olonisakindavid/FinalYearProject/incubator - 2.jpg

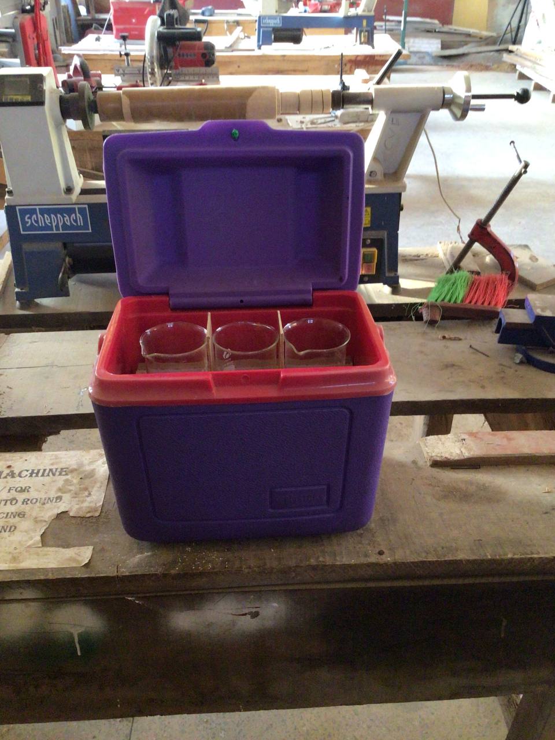
incubator - 2.jpg
