olonisakindavid/FinalYearProject/serial dht22 monitor.jpg

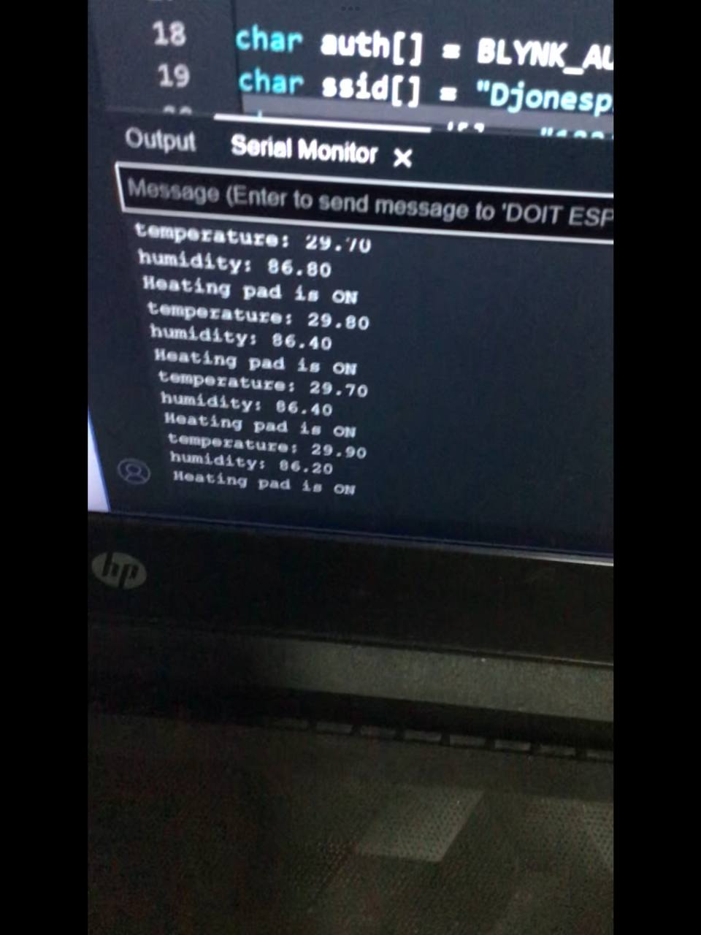
serial dht22 monitor.jpg
