olonisakindavid/FinalYearProject/side view.jpg

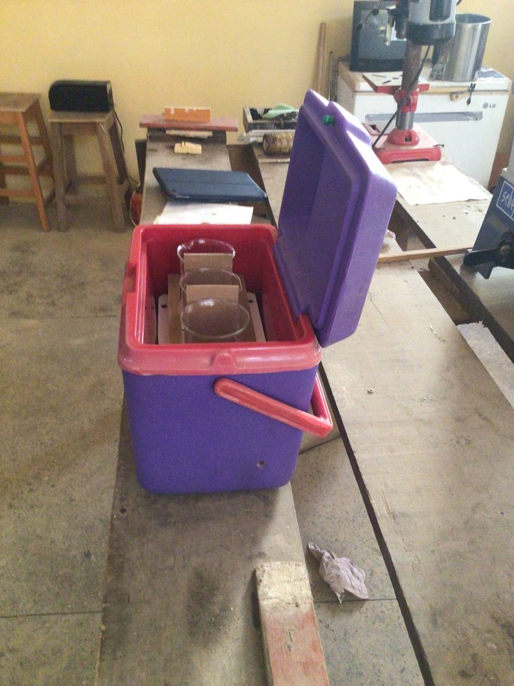
side view.jpg
