olonisakindavid/FinalYearProject/turnitin.png

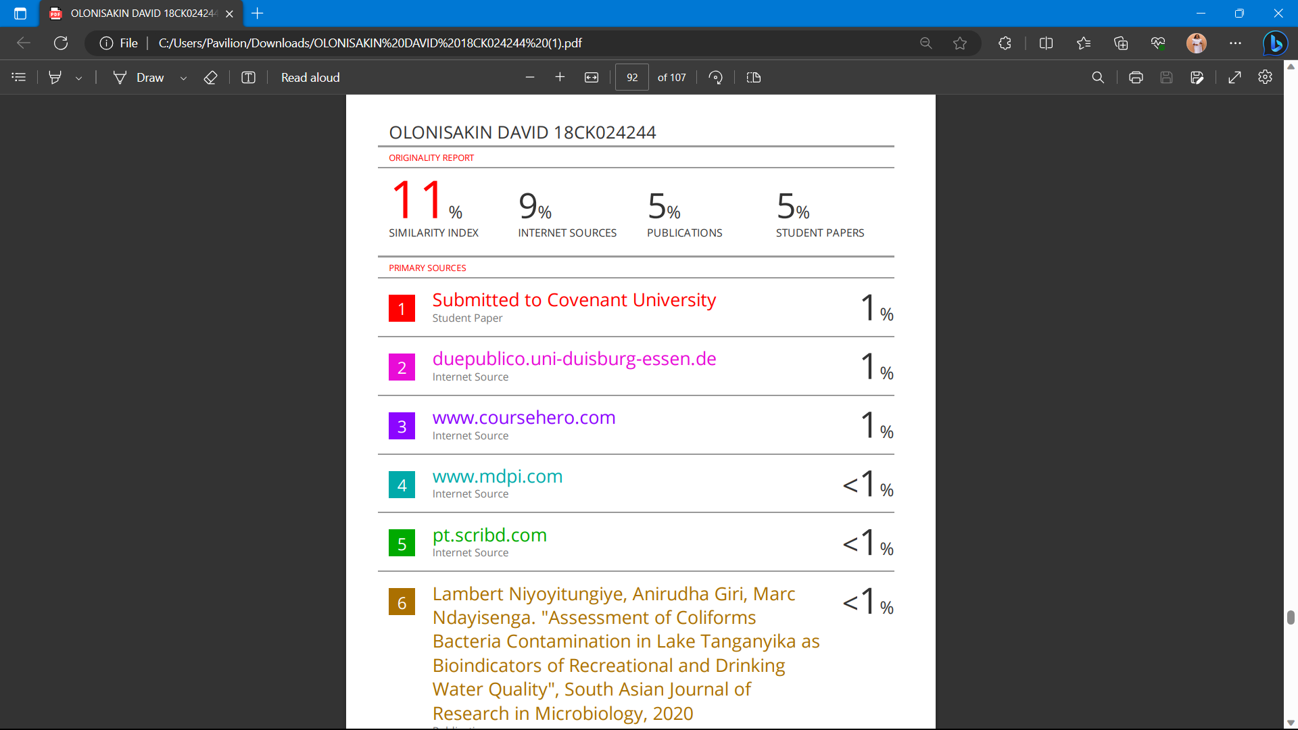
turnitin.png
