olonisakindavid/FinalYearProject/tested components.jpg

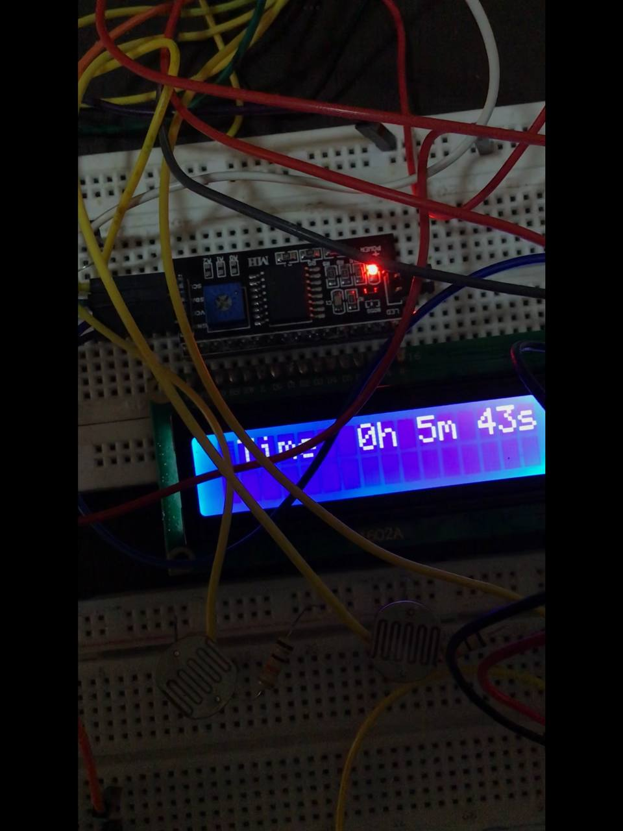
tested components.jpg
